jobitjoseph/Precision-Digital-Micro-Current-Meter/Images/Og/Precision Digital Micro Current Meter 3D2.png

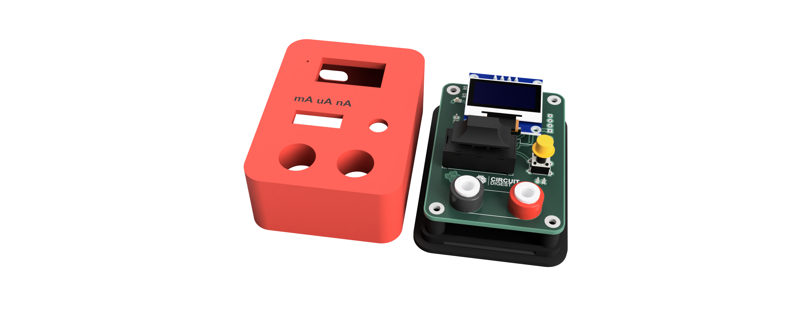
Images/Og/Precision Digital Micro Current Meter 3D2.png
