jobitjoseph/Precision-Digital-Micro-Current-Meter/Images/Precision Digital Micro Current Meter 3D2.png

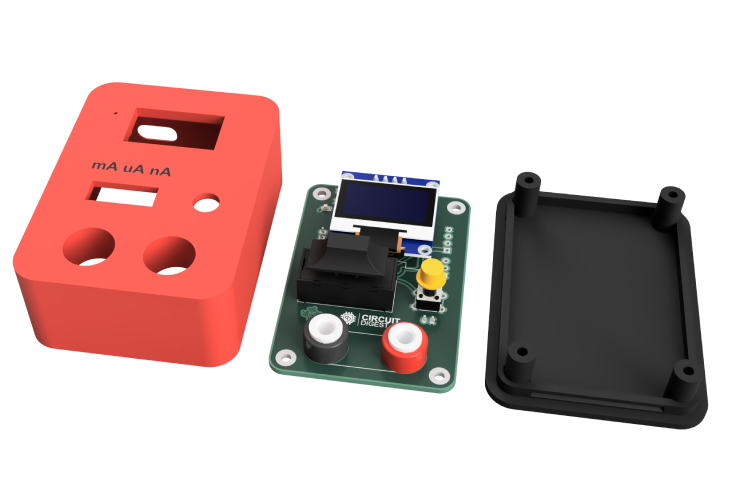
Images/Precision Digital Micro Current Meter 3D2.png
