jobitjoseph/Precision-Digital-Micro-Current-Meter/Images/Precision Digital Micro Current Meter Analog Front End.png

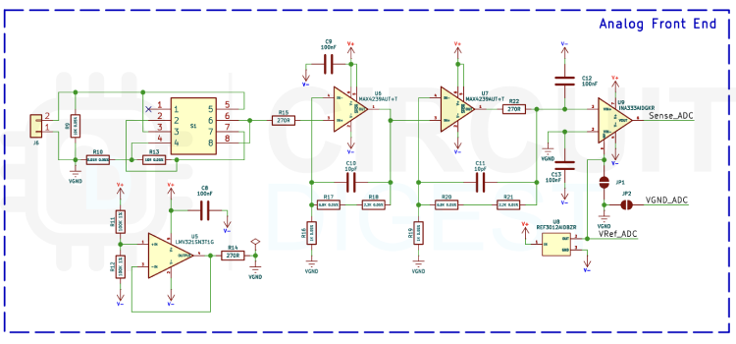
Images/Precision Digital Micro Current Meter Analog Front End.png
