jobitjoseph/Precision-Digital-Micro-Current-Meter/Images/Precision Digital Micro Current Meter Peripherals.png

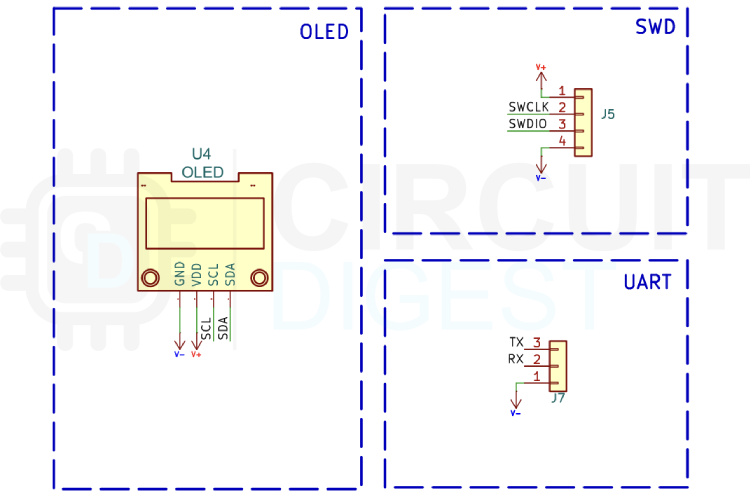
Images/Precision Digital Micro Current Meter Peripherals.png
