jobitjoseph/Precision-Digital-Micro-Current-Meter/Images/Precision Digital Micro Current Meter Power.png

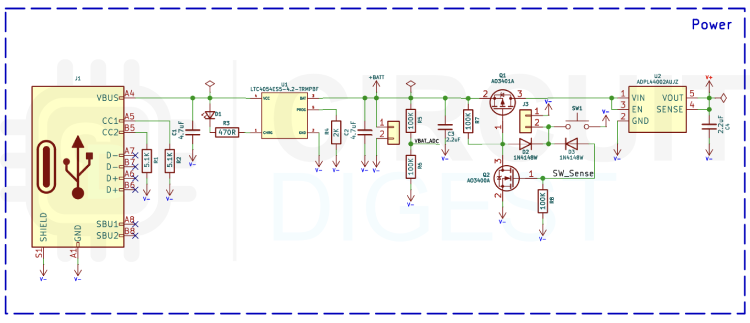
Images/Precision Digital Micro Current Meter Power.png
