jobitjoseph/Precision-Digital-Micro-Current-Meter/Images/Precision Digital Micro Current Meter Schematics750px.png

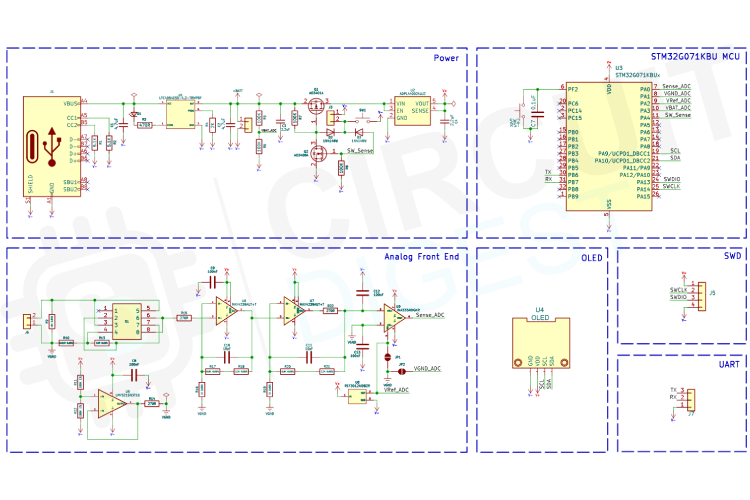
Images/Precision Digital Micro Current Meter Schematics750px.png
